ouser555/ergodashv99/ergodashv99組裝說明/pic/27.jpg

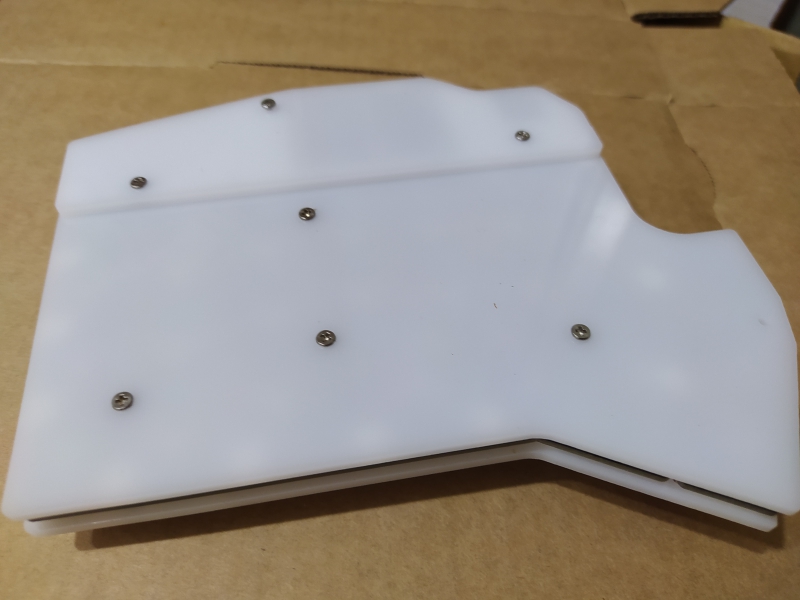
ergodashv99組裝說明/pic/27.jpg
