ouser555/ergodashv99/rev2組裝說明/pic/piiic (12).jpg

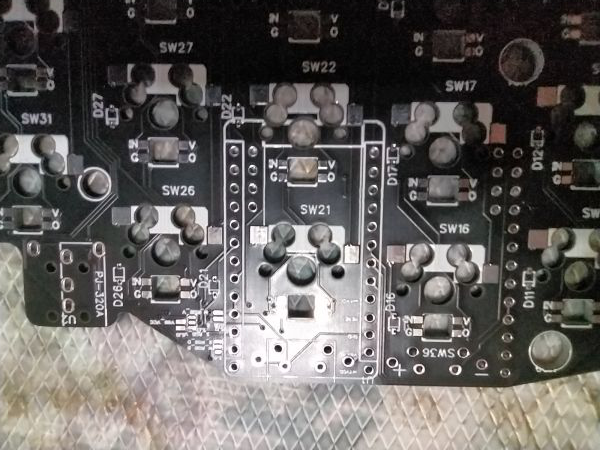
rev2組裝說明/pic/piiic (12).jpg
