ouser555/ergodashv99/rev2組裝說明/pic/piiic (44).jpg

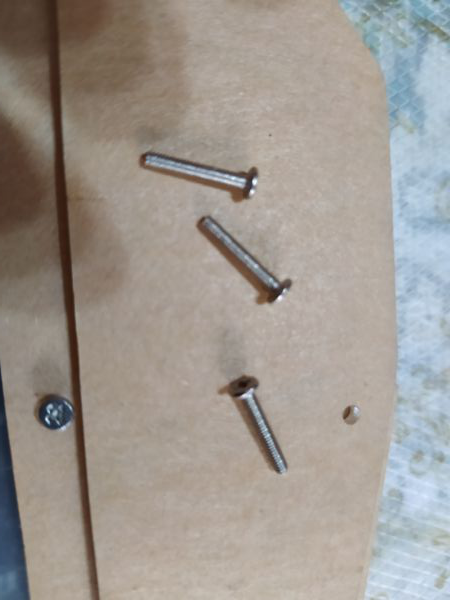
rev2組裝說明/pic/piiic (44).jpg
